ATGr8/CubeSat-EPS/EPS-sims/MPPT-v2.asc

C1: cap; 1µ
C2: cap; 10µ
C3: cap; 1µ
C4: cap; 10µ
C5: cap; 3.3µ
C6: cap; 33p
C7: cap; 1µ
D1: schottky
D2: schottky
D3: schottky
D4: schottky
D5: schottky
L1: ind; 10µ
R1: res; 100k
R2: res; 530k
R3: res; 500k
R4: res; 330k
R5: res; 51k
R6: res; 750k
R7: res; 250k
R8: res; 100k
R9: res; 50m
U1: LT3652HV
U2: LT3012
V1: voltage; 12; Rser=1
V2: voltage; PULSE(5 8 2m 1n 1n 2 4)
Named nets: 0, vload, Vreg5
.tran 0 10s 0s
